M1r3o/Laser-Harp-Project/Image Archive/calcul_0002.pdf

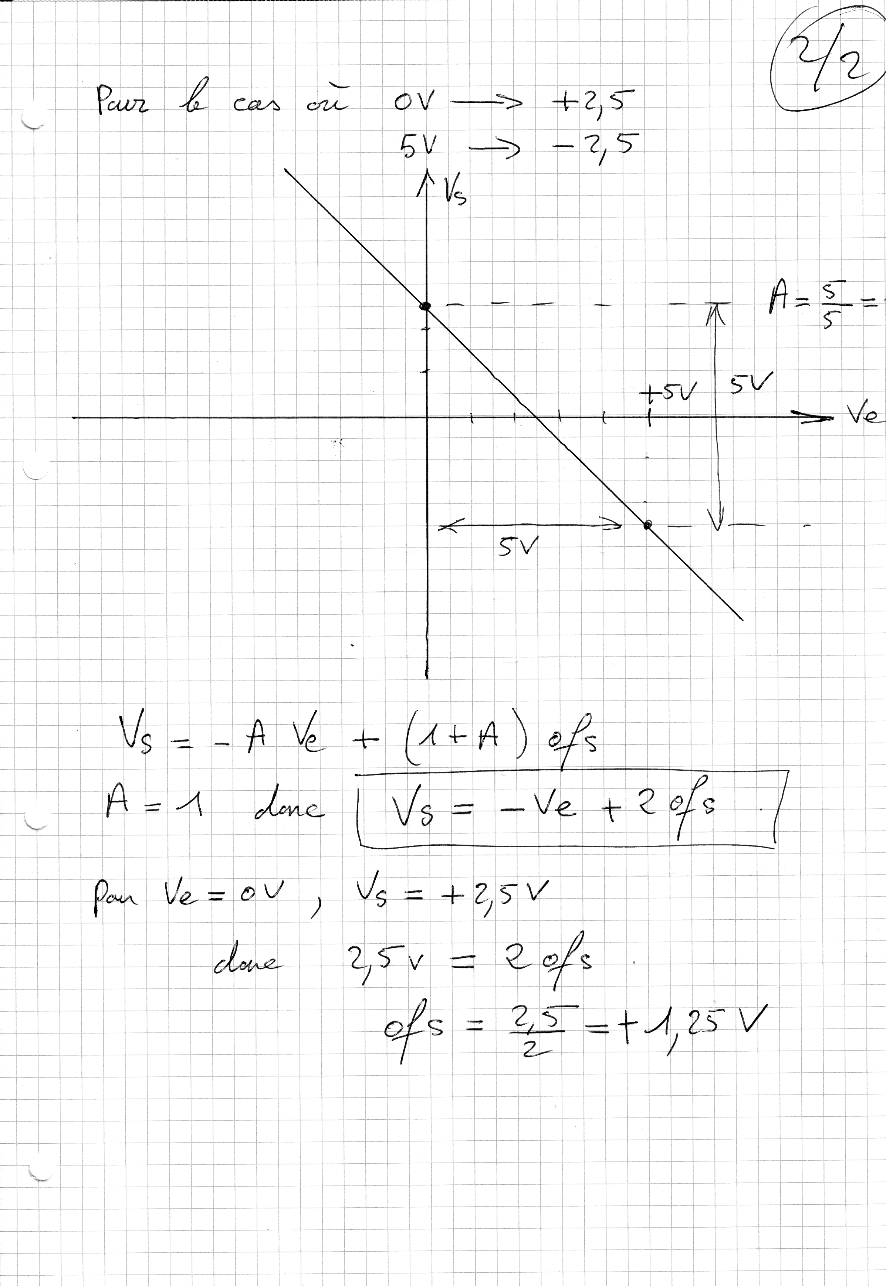
[picture p3: page 1]
